SOURCE-Platform/deepreal/blender/refinements/r26/README.md

# R26 contoured roof edge

The rear roof reaches forward as a tapered leading edge while leaving the drum crowns exposed. Its underside follows the upper rear drum arc with a nominal 0.5 mm radial gap. The outer supports now reveal a curved opening at the drum ends; the center island remains between the two drums. The enclosure top and drum crowns are level at 32 mm.

## Files

- `deepreal-contoured-roof-edge-r26.blend` — editable exterior model.
- `deepreal-website-presentation-r26.blend` — model with website camera and lights.
- `r26-website-hero-dark.png` and `r26-website-hero-transparent.png` — website renders.
- `r26-roof-detail.png` — close side view of the contoured transition.
- `r26-side-preview.png` and `r26-above-preview.png` — shape review views.
- `r26-enclosure-check.json` — topology, gap profile, and sampled pose check.

This is an appearance model. The gap is visual clearance, not a validated dust seal; parting seams and fabrication tolerance remain for later work.
