SOURCE-Platform/deepreal/blender/refinements/r20/r20-interaction-desk-coverage.png

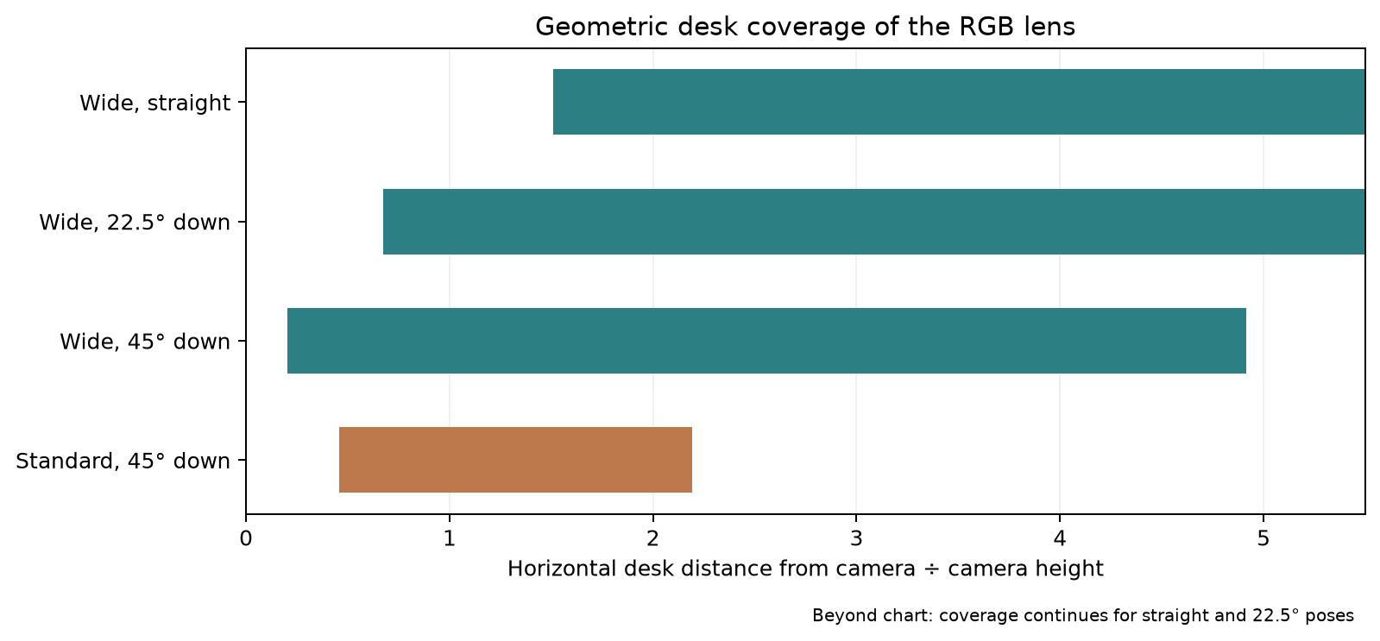
blender/refinements/r20/r20-interaction-desk-coverage.png
