SOURCE-Platform/deepreal/blender/refinements/r20/r20-wide-envelope-vs-carrier.png

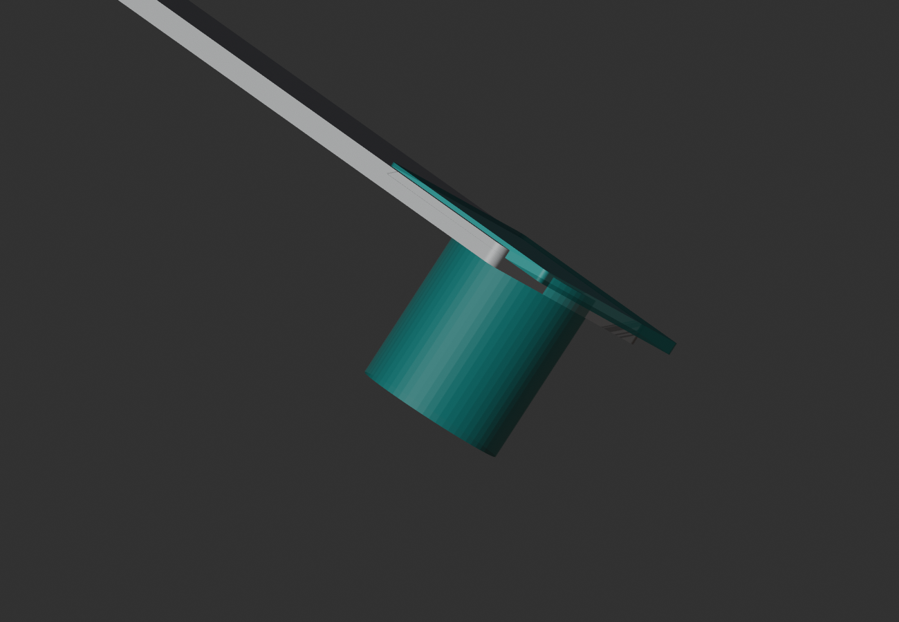
blender/refinements/r20/r20-wide-envelope-vs-carrier.png
