SOURCE-Platform/deepreal/blender/refinements/r21/r21-drive-detail-preview.png

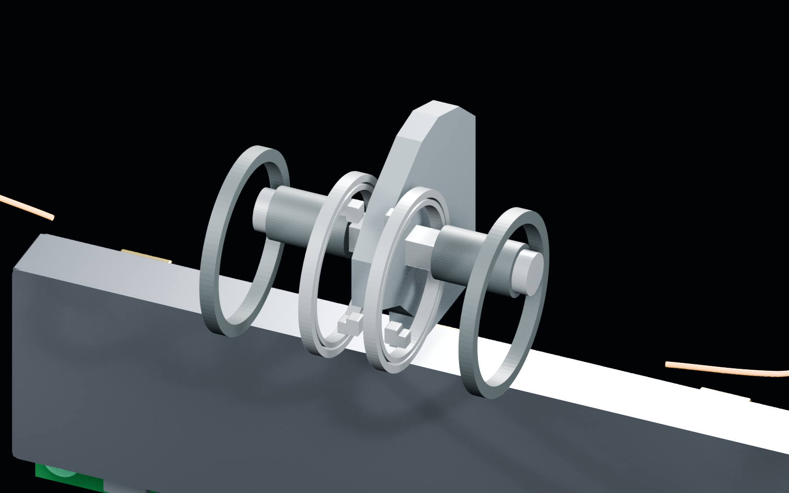
blender/refinements/r21/r21-drive-detail-preview.png
