SOURCE-Platform/deepreal/blender/refinements/r21/r21-exterior-preview.png

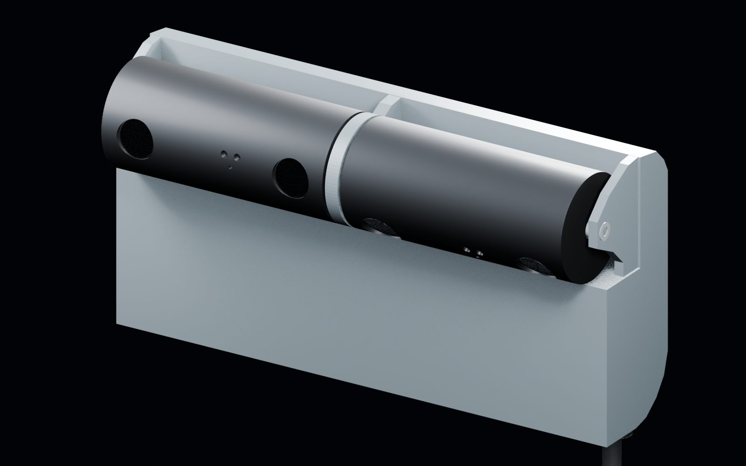
blender/refinements/r21/r21-exterior-preview.png
