SOURCE-Platform/deepreal/blender/refinements/r21/r21-front-preview.png

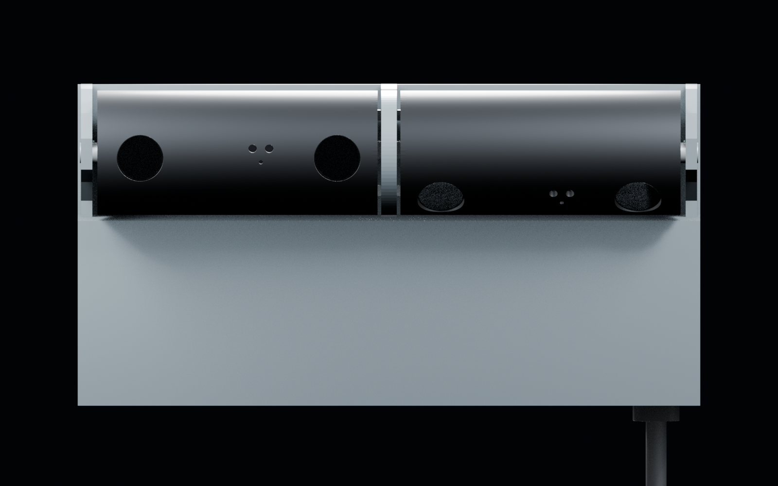
blender/refinements/r21/r21-front-preview.png
