SOURCE-Platform/deepreal/blender/refinements/r21/r21-low-pose-preview.png

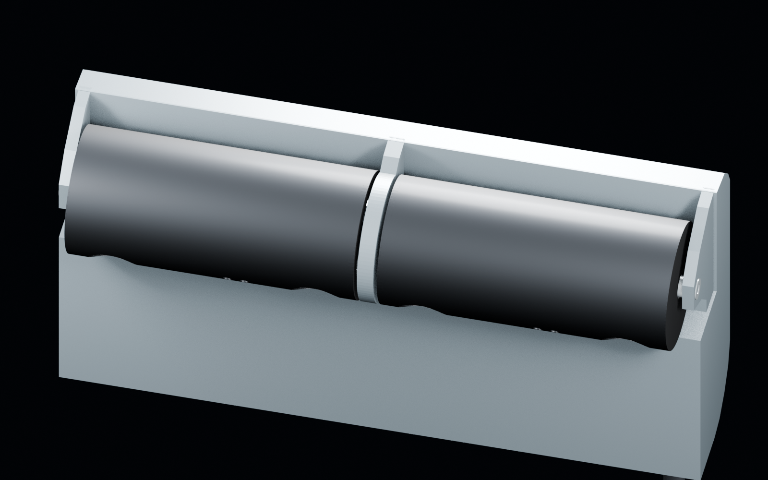
blender/refinements/r21/r21-low-pose-preview.png
