SOURCE-Platform/deepreal/blender/refinements/r22/r22-side-preview.png

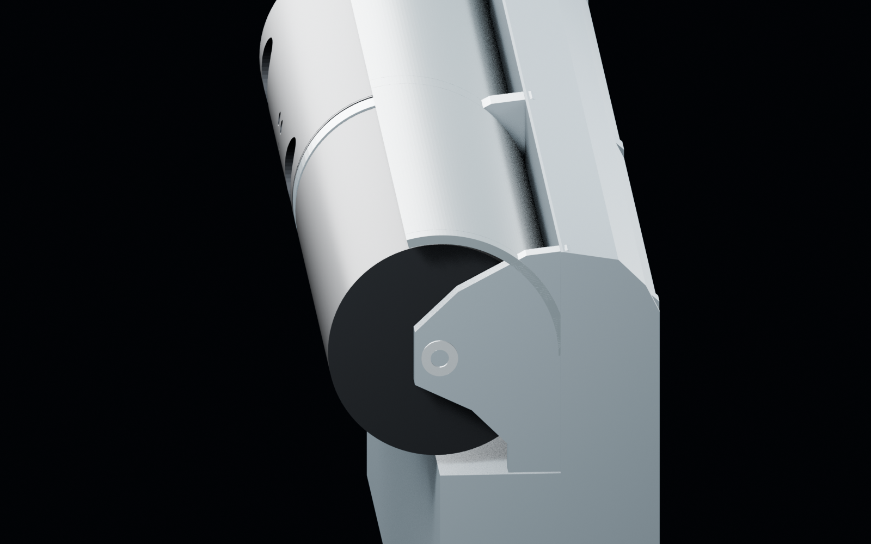
blender/refinements/r22/r22-side-preview.png
