SOURCE-Platform/deepreal/blender/refinements/r23/r23-side-preview.png

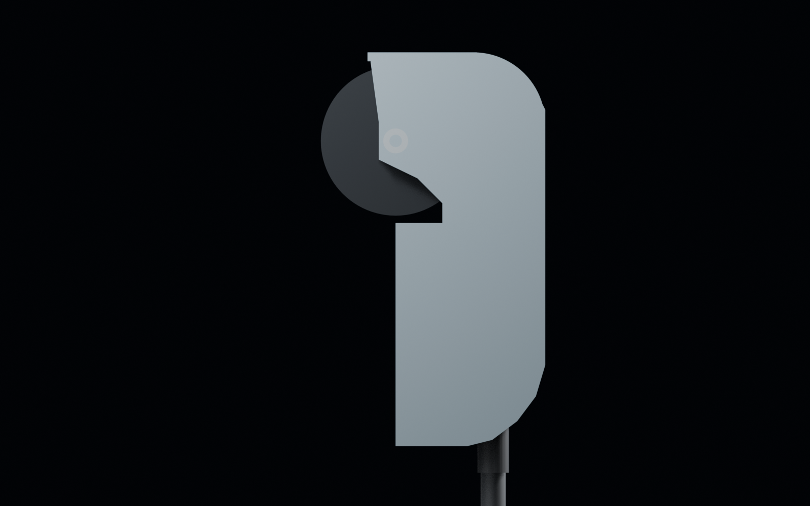
blender/refinements/r23/r23-side-preview.png
