SOURCE-Platform/deepreal/blender/refinements/r24/r24-above-preview.png

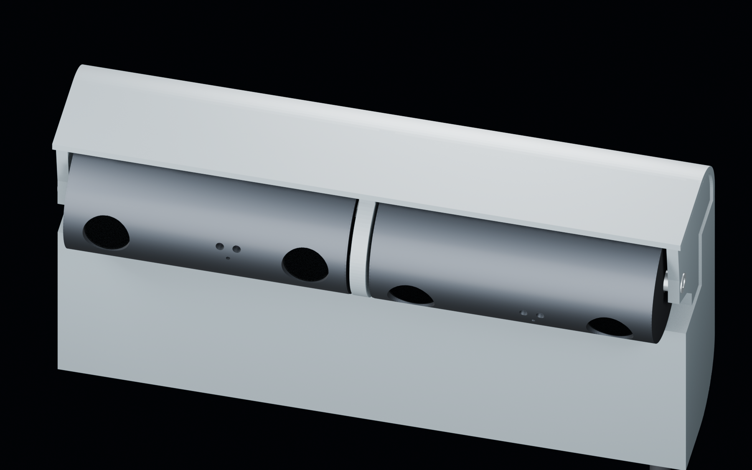
blender/refinements/r24/r24-above-preview.png
