SOURCE-Platform/deepreal/blender/refinements/r24/r24-front-preview.png

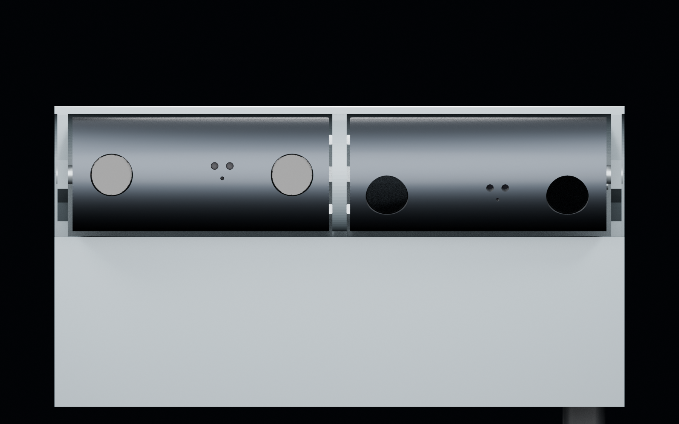
blender/refinements/r24/r24-front-preview.png
