SOURCE-Platform/deepreal/blender/refinements/r24/r24-website-hero-dark.png

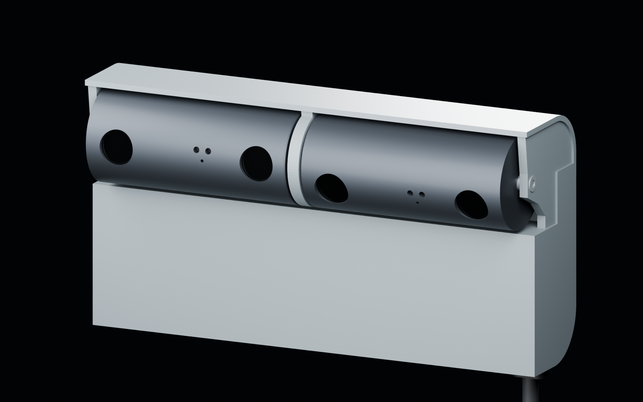
blender/refinements/r24/r24-website-hero-dark.png
