SOURCE-Platform/deepreal/blender/refinements/r24/r24-website-hero-transparent.png

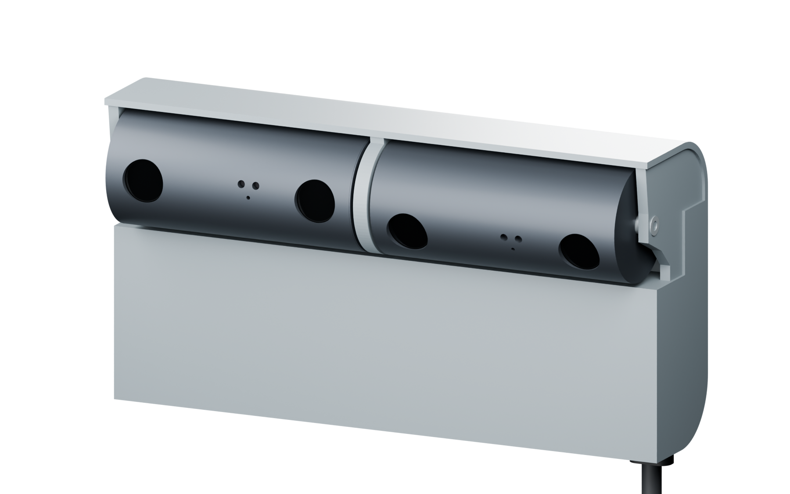
blender/refinements/r24/r24-website-hero-transparent.png
