SOURCE-Platform/deepreal/blender/refinements/r26/r26-roof-detail.png

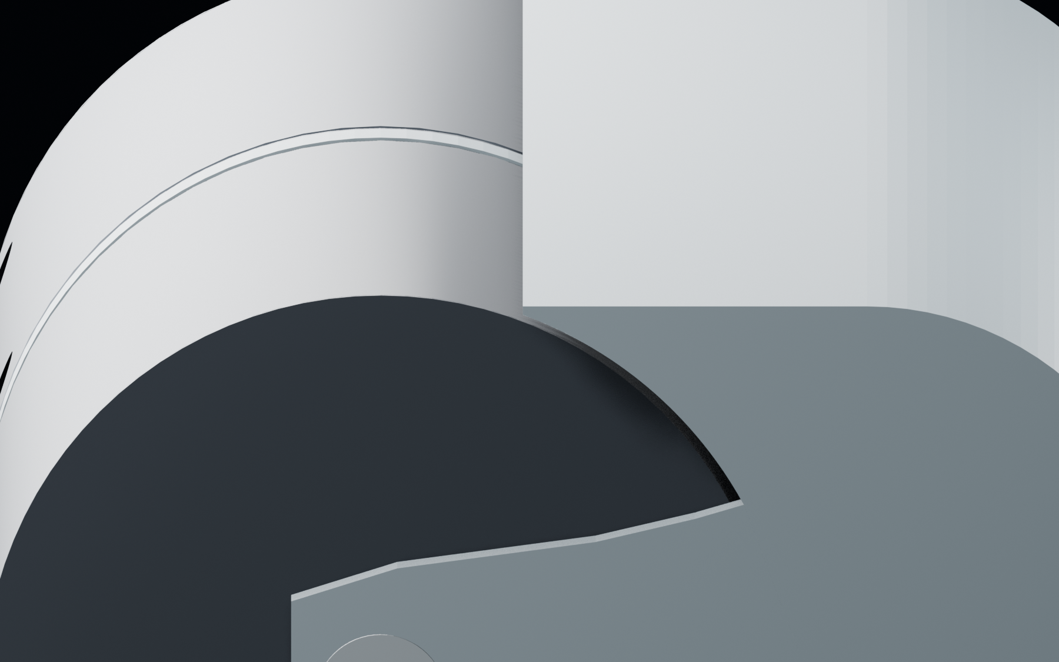
blender/refinements/r26/r26-roof-detail.png
