SOURCE-Platform/deepreal/blender/refinements/r26/r26-shell-only-front.png

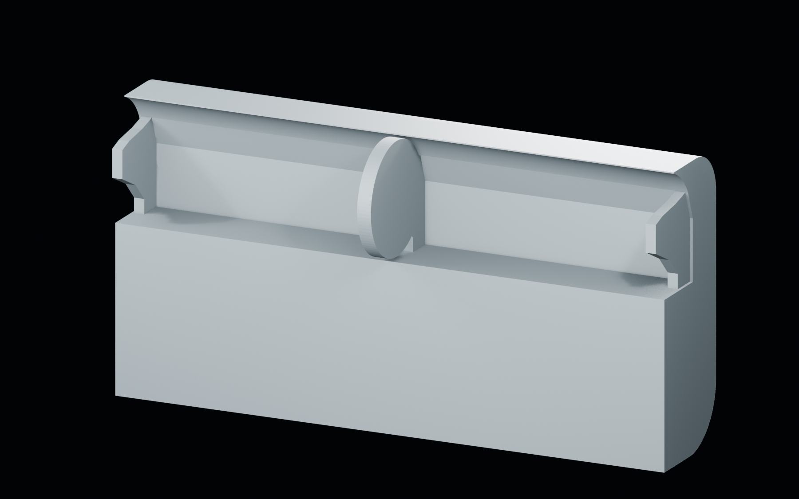
blender/refinements/r26/r26-shell-only-front.png
