SOURCE-Platform/deepreal/blender/refinements/r26/r26-shell-only-low.png

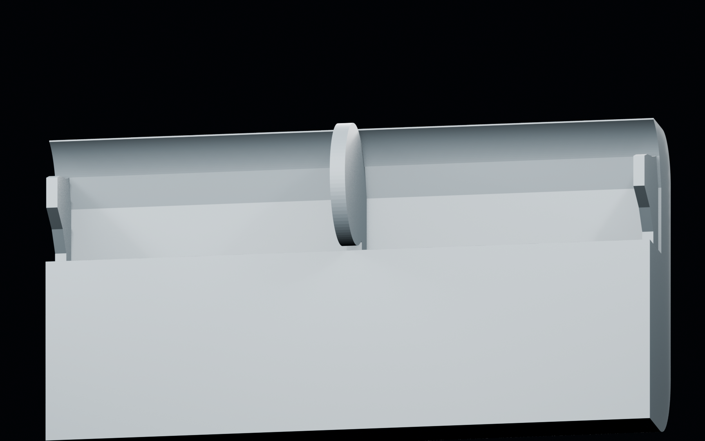
blender/refinements/r26/r26-shell-only-low.png
