SOURCE-Platform/deepreal/blender/refinements/r28/r28-connected-shell-low.png

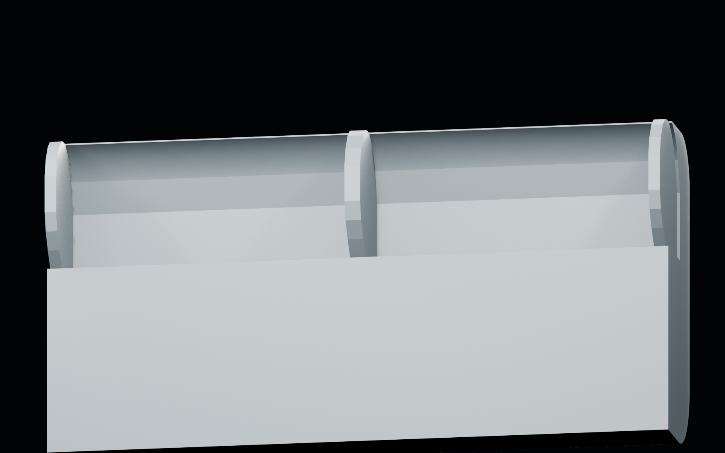
blender/refinements/r28/r28-connected-shell-low.png
