SOURCE-Platform/deepreal/blender/refinements/r28/r28-connected-shell.png

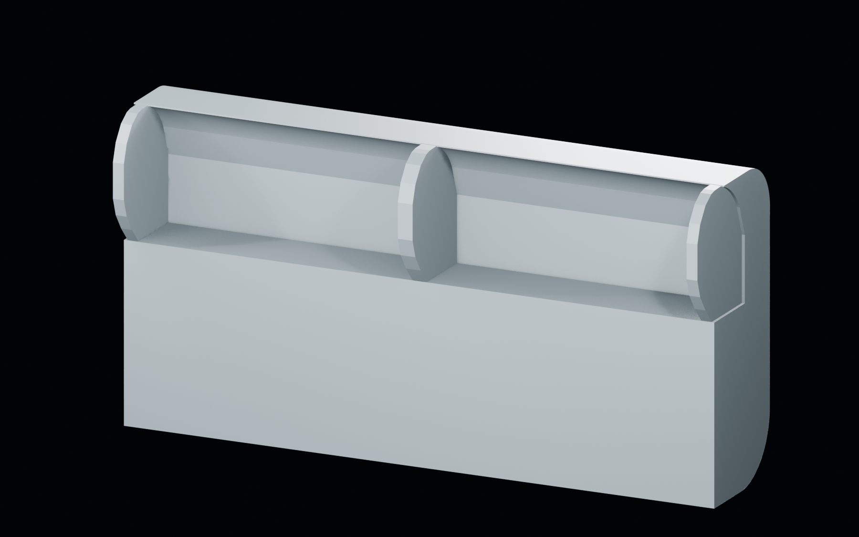
blender/refinements/r28/r28-connected-shell.png
