SOURCE-Platform/deepreal/blender/refinements/r28/r28-three-dividers-shell.png

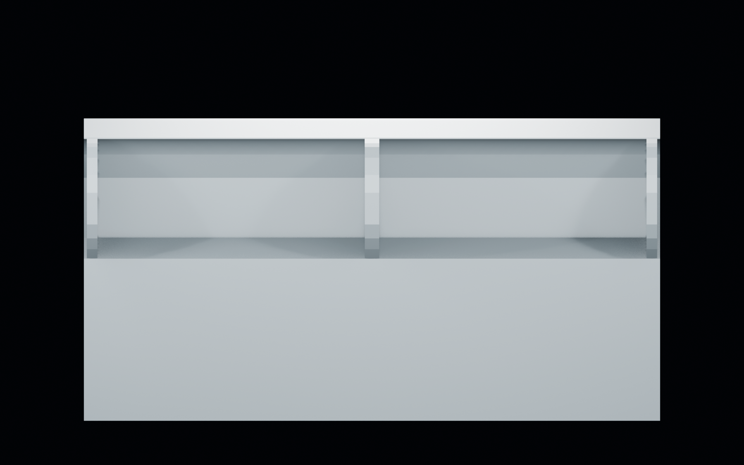
blender/refinements/r28/r28-three-dividers-shell.png
