SOURCE-Platform/deepreal/blender/refinements/r29/r29-center-divider-detail.png

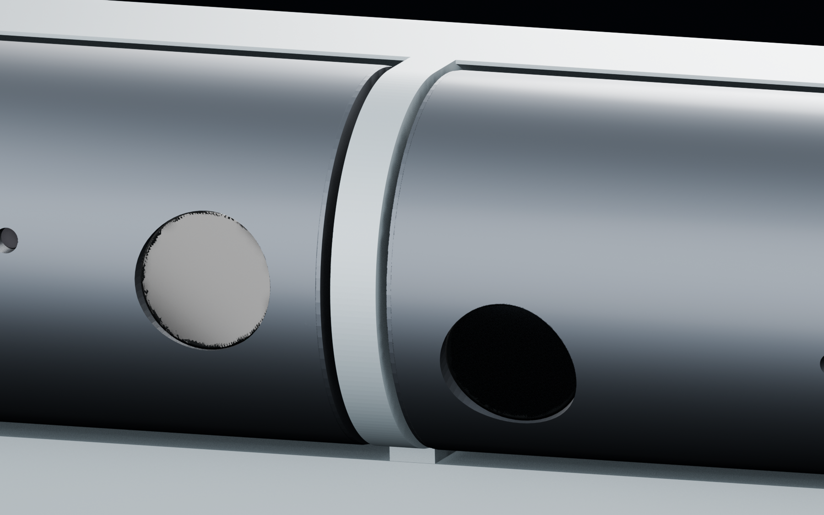
blender/refinements/r29/r29-center-divider-detail.png
