SOURCE-Platform/deepreal/blender/refinements/r29/r29-connected-shell-low.png

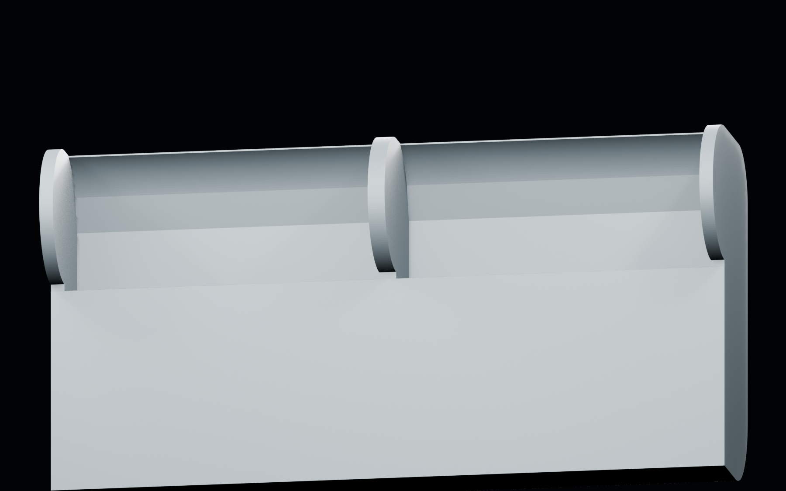
blender/refinements/r29/r29-connected-shell-low.png
