SOURCE-Platform/deepreal/blender/refinements/r29/r29-right-side-detail.png

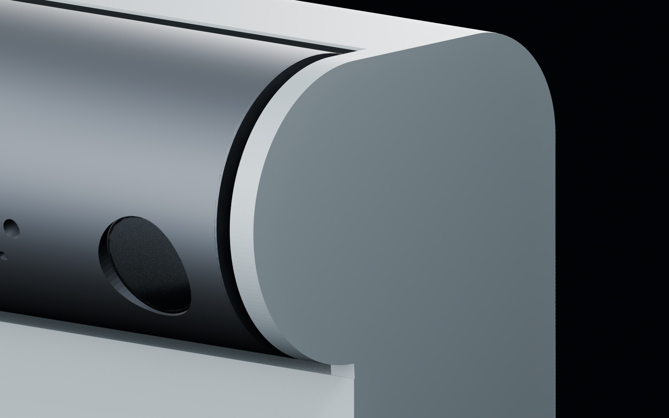
blender/refinements/r29/r29-right-side-detail.png
