SOURCE-Platform/deepreal/blender/refinements/r29/r29-three-dividers-shell.png

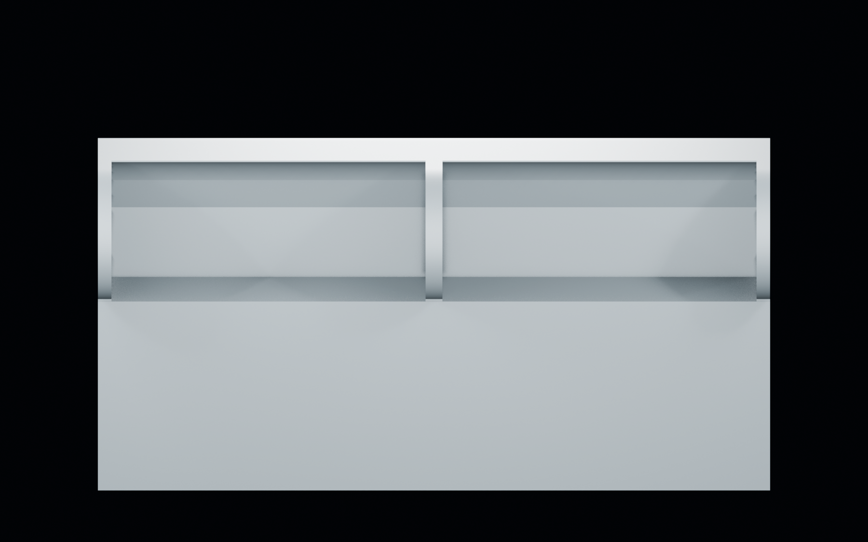
blender/refinements/r29/r29-three-dividers-shell.png
