SOURCE-Platform/deepreal/blender/refinements/r30/r30-ledge-detail.png

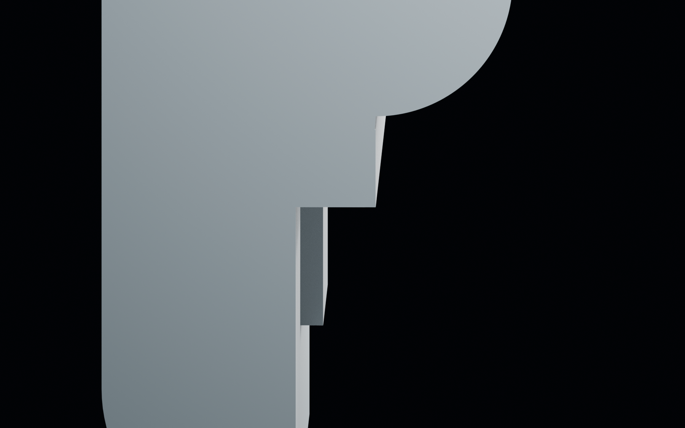
blender/refinements/r30/r30-ledge-detail.png
