SOURCE-Platform/deepreal/blender/refinements/r30/r30-monitor-mount-section.png

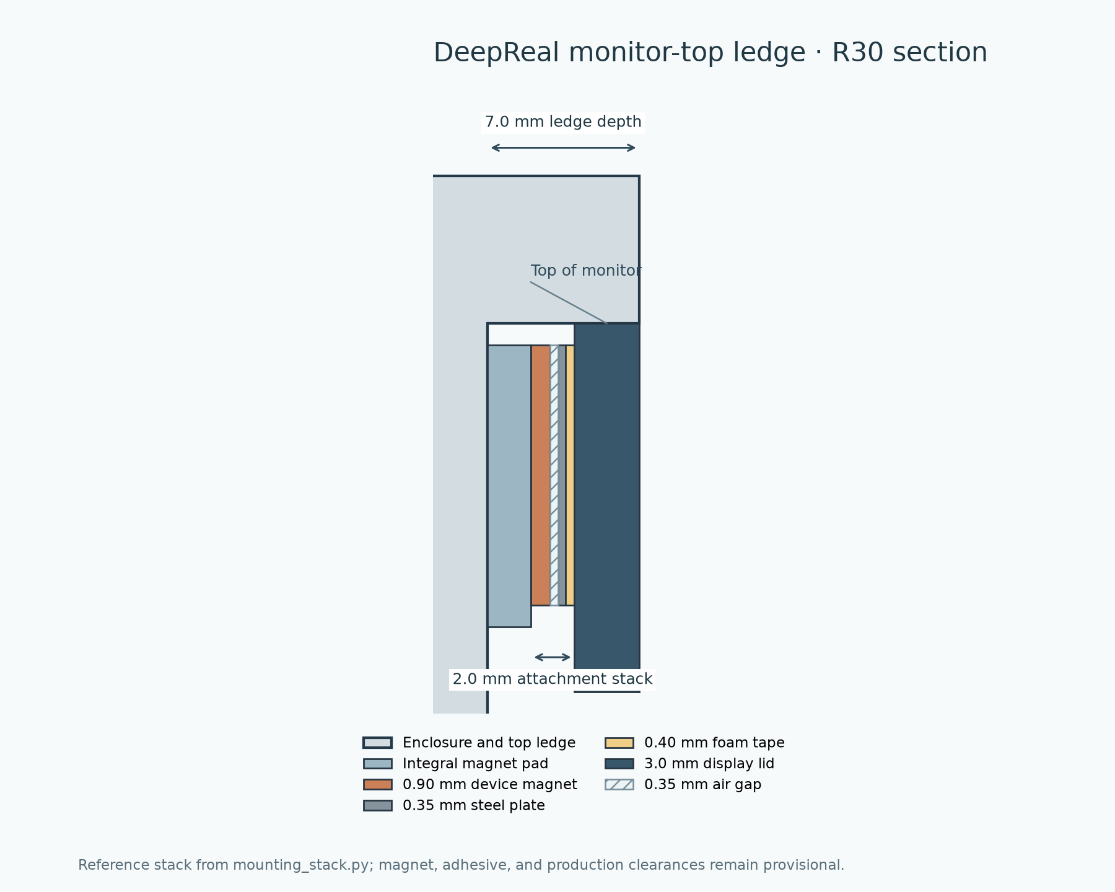
blender/refinements/r30/r30-monitor-mount-section.png
