SOURCE-Platform/deepreal/blender/refinements/r30/r30-side-profile.png

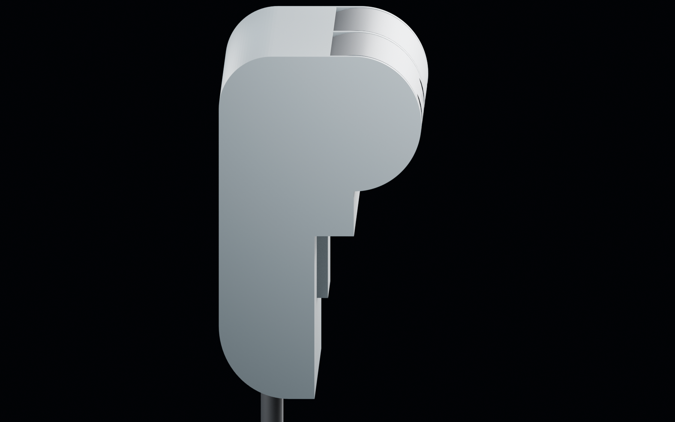
blender/refinements/r30/r30-side-profile.png
