SOURCE-Platform/deepreal/blender/refinements/r31/r31-attachment-layers-exploded.png

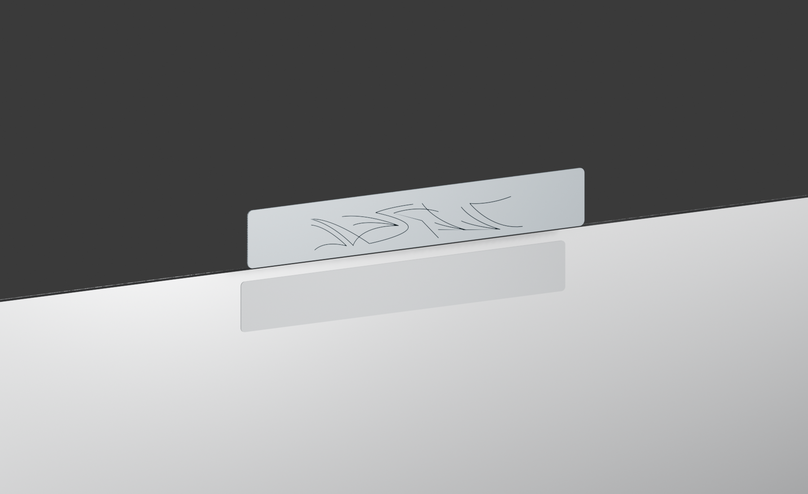
blender/refinements/r31/r31-attachment-layers-exploded.png
