SOURCE-Platform/deepreal/blender/refinements/r31/r31-full-width-plate.png

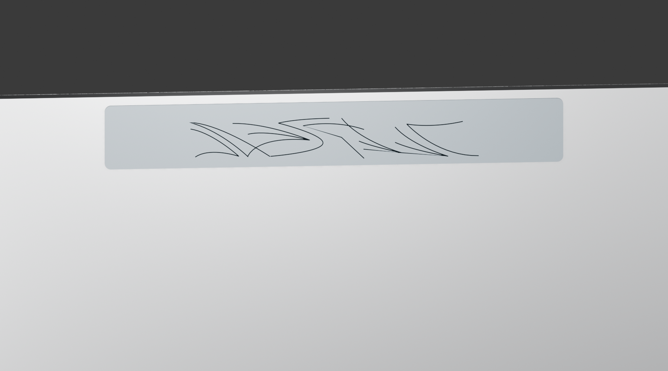
blender/refinements/r31/r31-full-width-plate.png
