SOURCE-Platform/deepreal/blender/refinements/r31/r31-laptop-back.png

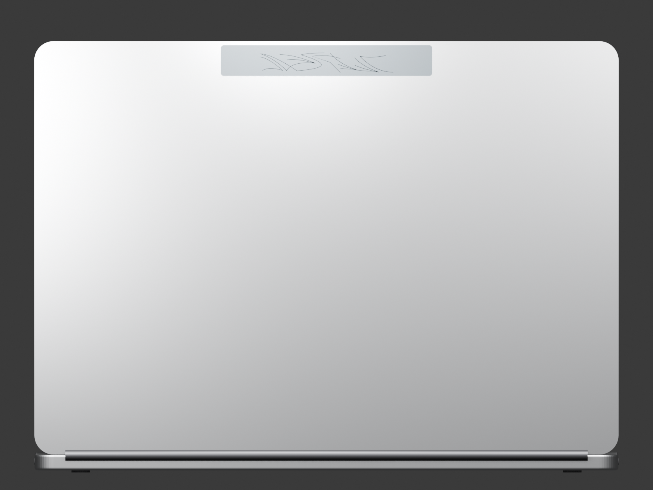
blender/refinements/r31/r31-laptop-back.png
