SOURCE-Platform/deepreal/blender/refinements/r32/r32-groove-shadow-detail.png

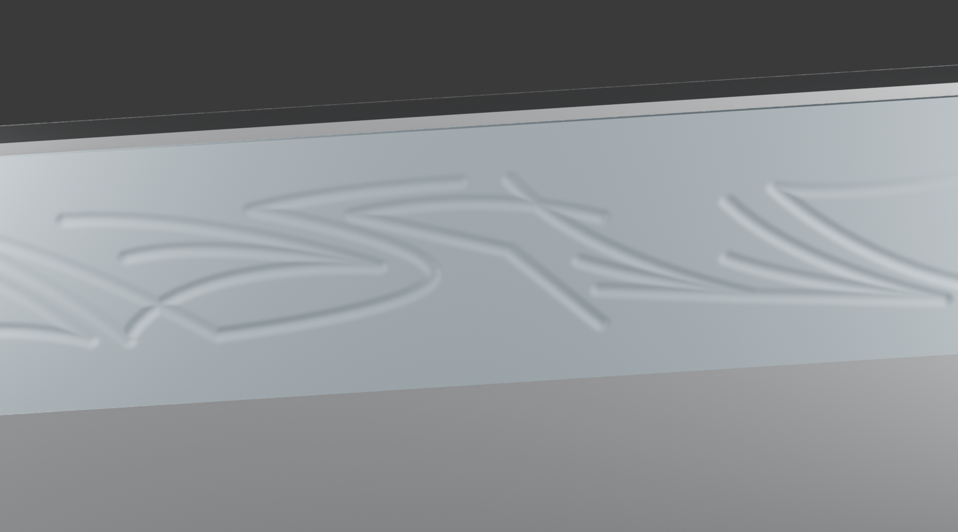
blender/refinements/r32/r32-groove-shadow-detail.png
