SOURCE-Platform/deepreal/blender/refinements/r32/r32-laptop-back.png

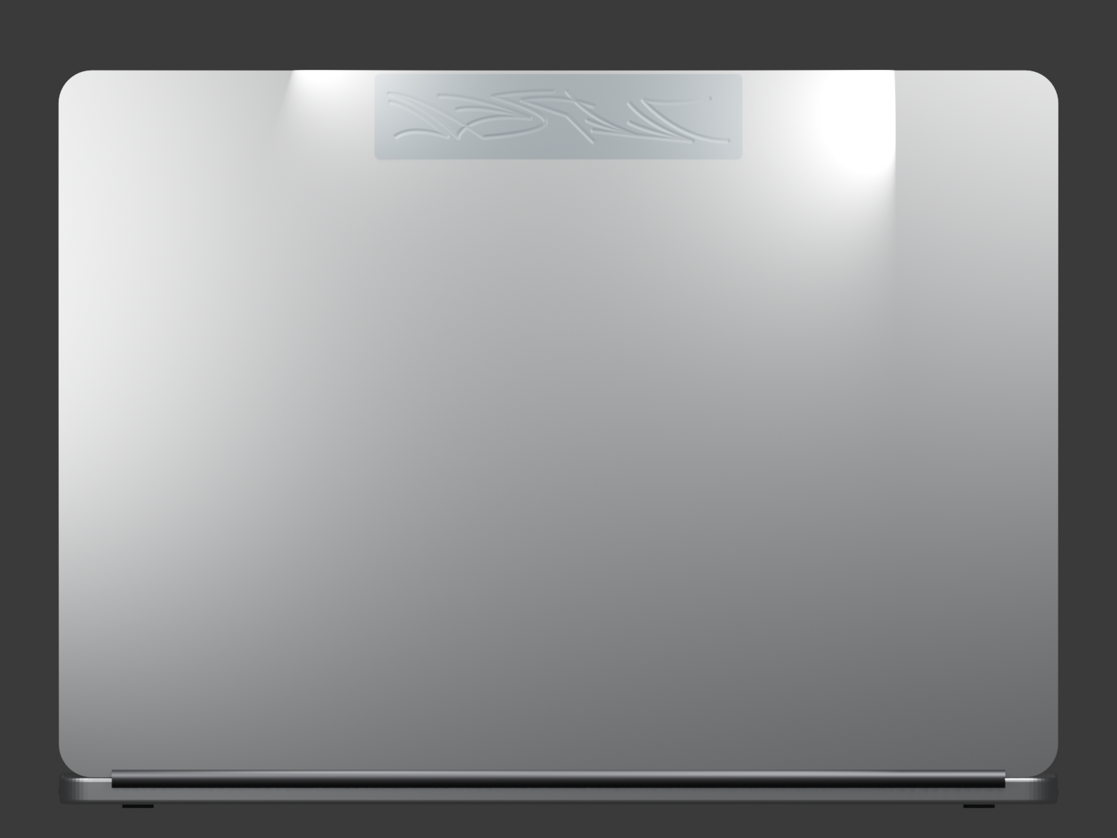
blender/refinements/r32/r32-laptop-back.png
