SOURCE-Platform/deepreal/blender/refinements/r32/r32-tall-pressed-plate.png

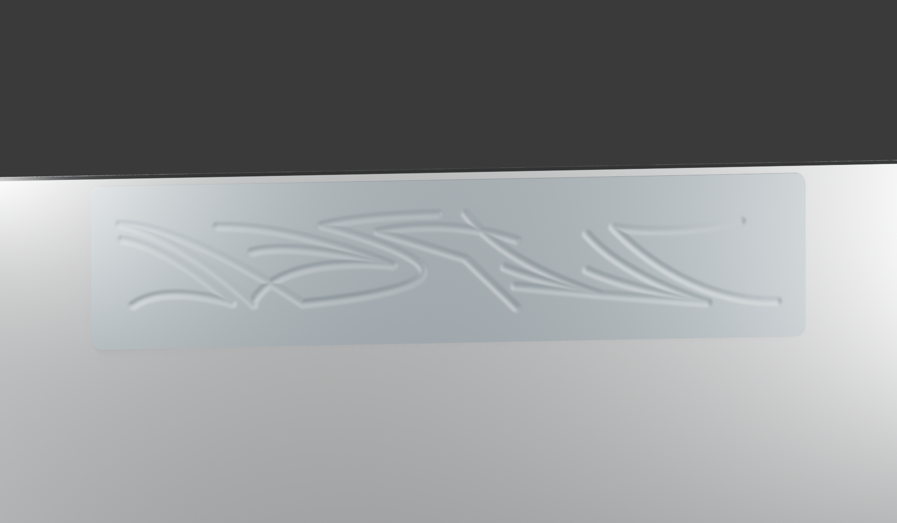
blender/refinements/r32/r32-tall-pressed-plate.png
