SOURCE-Platform/deepreal/blender/refinements/r33/r33-moving-sheen-preview.gif

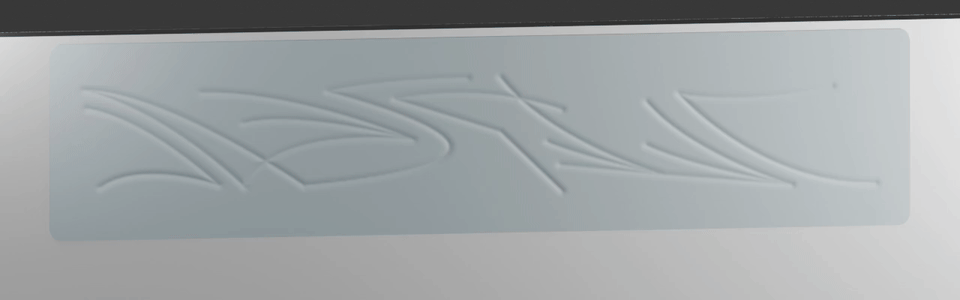
blender/refinements/r33/r33-moving-sheen-preview.gif
