SOURCE-Platform/deepreal/blender/refinements/r33/r33-profile-comparison.png

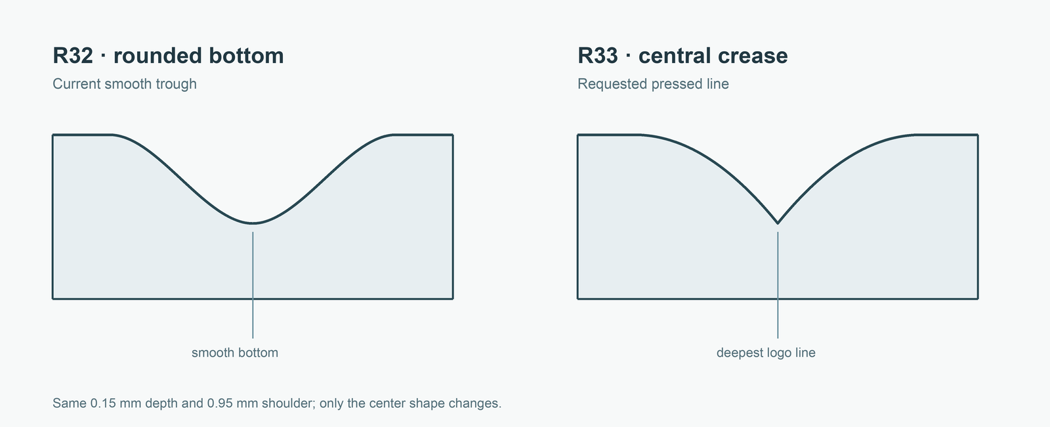
blender/refinements/r33/r33-profile-comparison.png
