SOURCE-Platform/deepreal/blender/refinements/r34/r34-inner-flex-detail.png

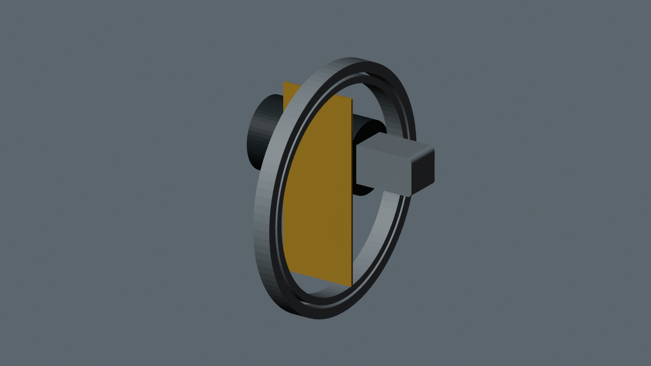
blender/refinements/r34/r34-inner-flex-detail.png
