SOURCE-Platform/deepreal/blender/refinements/r34/r34-mechanism-study.png

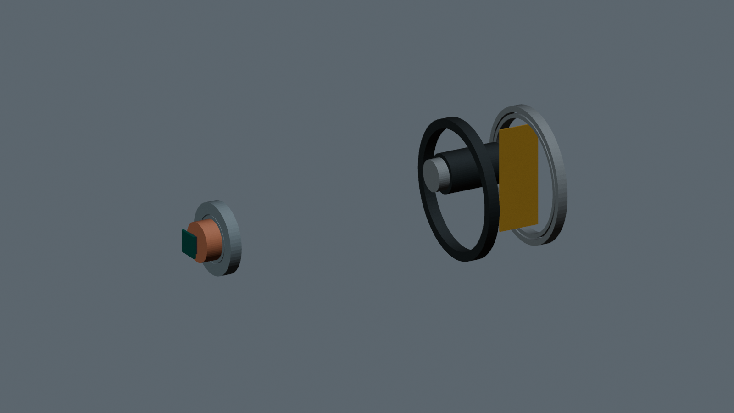
blender/refinements/r34/r34-mechanism-study.png
