SOURCE-Platform/deepreal/blender/refinements/r34/r34-outer-encoder-detail.png

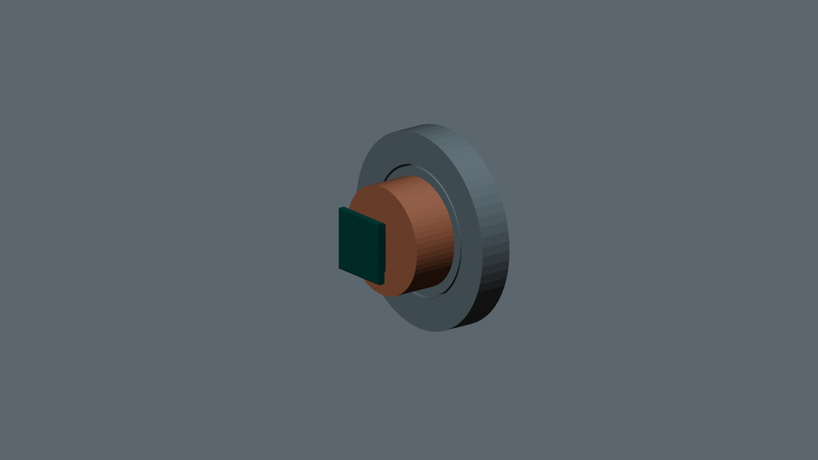
blender/refinements/r34/r34-outer-encoder-detail.png
