SOURCE-Platform/deepreal/blender/refinements/r35/r35-flex-center-conflict.png

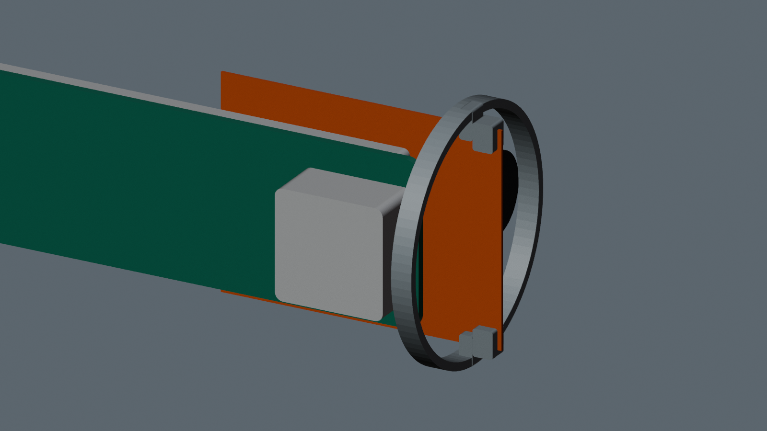
blender/refinements/r35/r35-flex-center-conflict.png
