SOURCE-Platform/deepreal/blender/refinements/r35/r35-flex-up45-conflict.png

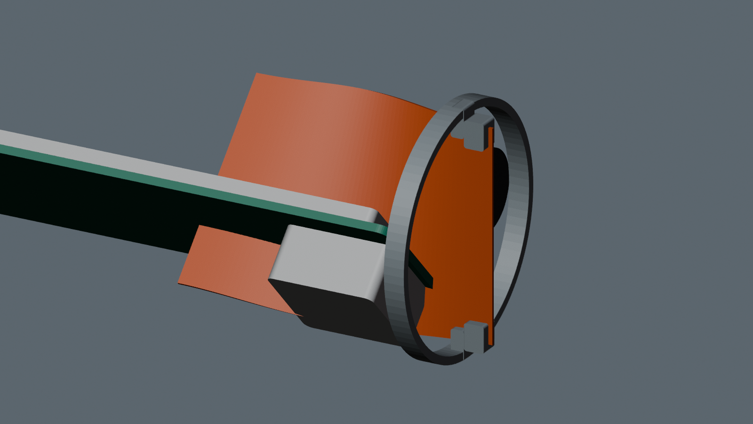
blender/refinements/r35/r35-flex-up45-conflict.png
