SOURCE-Platform/deepreal/blender/refinements/r35/r35-outer-load-path.png

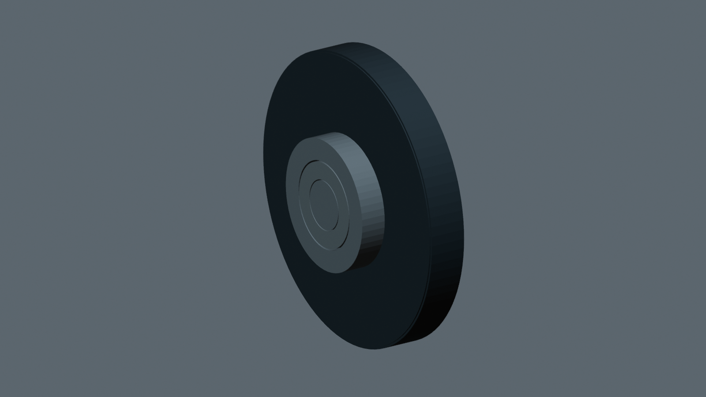
blender/refinements/r35/r35-outer-load-path.png
