SOURCE-Platform/deepreal/blender/refinements/r36/r36-bearing-window-end.png

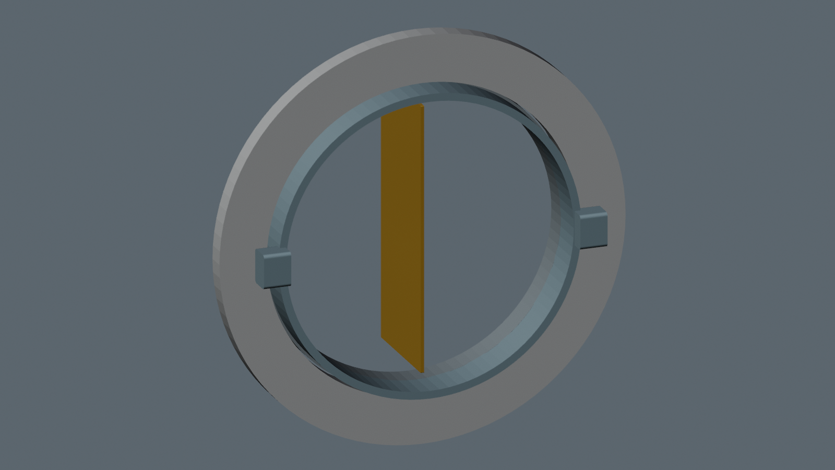
blender/refinements/r36/r36-bearing-window-end.png
