SOURCE-Platform/deepreal/blender/refinements/r36/r36-bearing-window-side.png

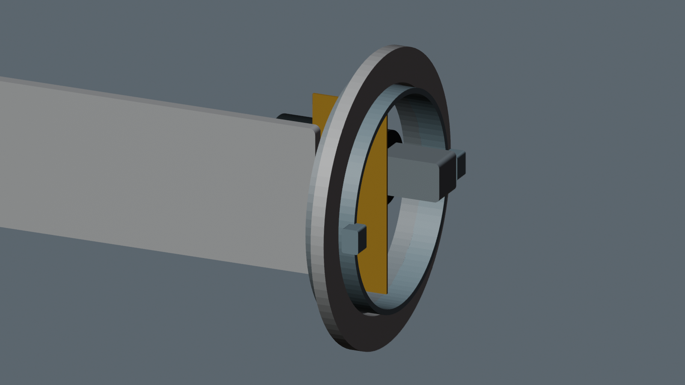
blender/refinements/r36/r36-bearing-window-side.png
