SOURCE-Platform/deepreal/blender/refinements/r37/r37-rear-volume-internal.png

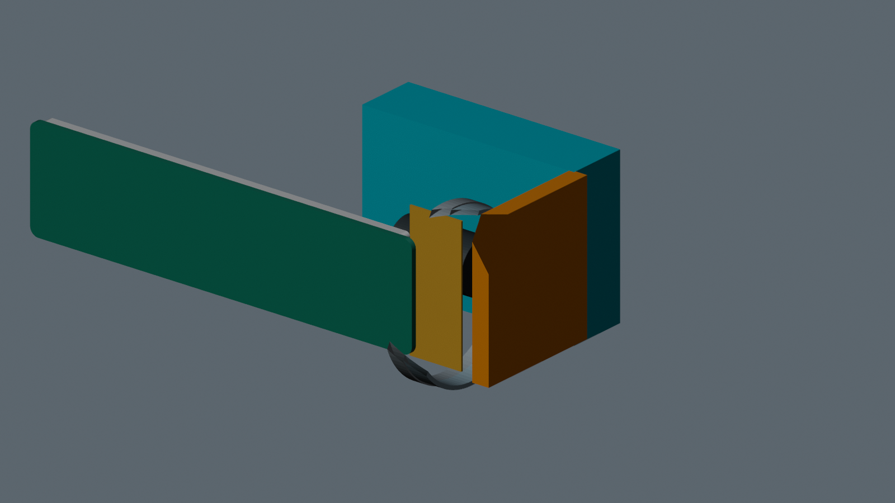
blender/refinements/r37/r37-rear-volume-internal.png
