SOURCE-Platform/deepreal/blender/refinements/r38/r38-usb-plug-detail.png

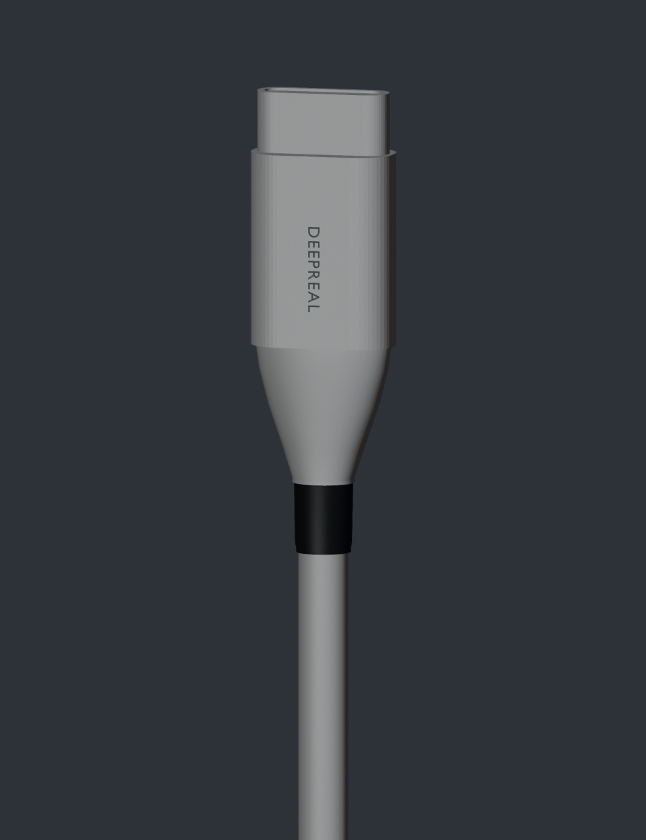
blender/refinements/r38/r38-usb-plug-detail.png
