SOURCE-Platform/deepreal/docs/design/blender-electronics-shield.png

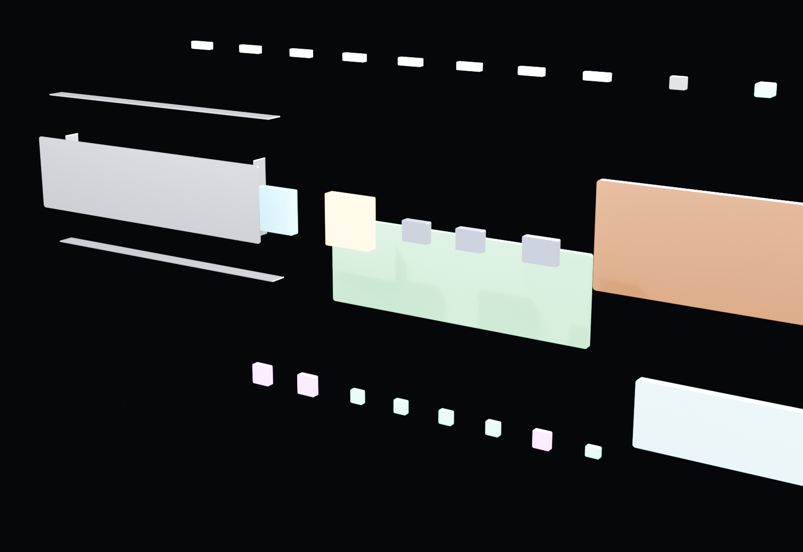
docs/design/blender-electronics-shield.png
