SOURCE-Platform/deepreal/docs/design/blender-four-view-overview.png

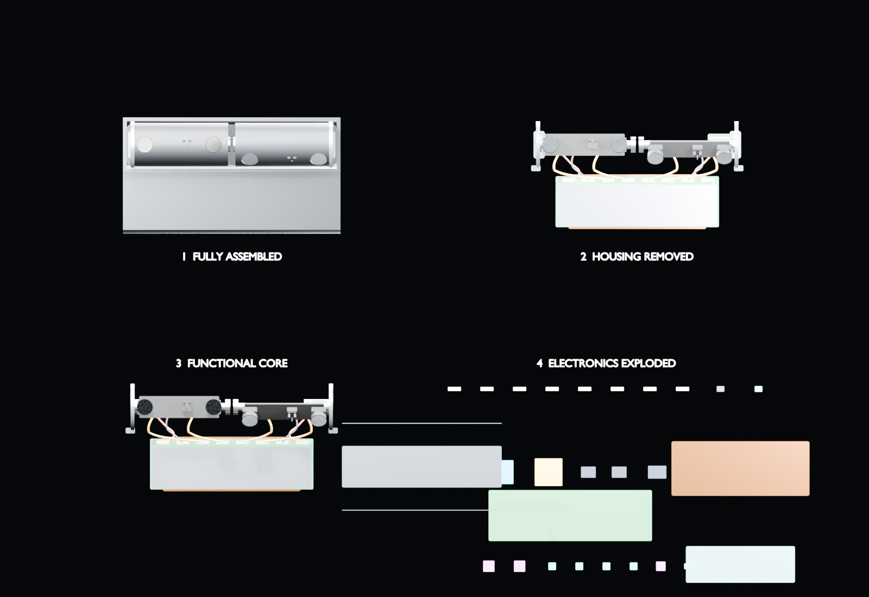
docs/design/blender-four-view-overview.png
