SOURCE-Platform/deepreal/references/components/datasheets/robotis-xl330-m288-drawing.png

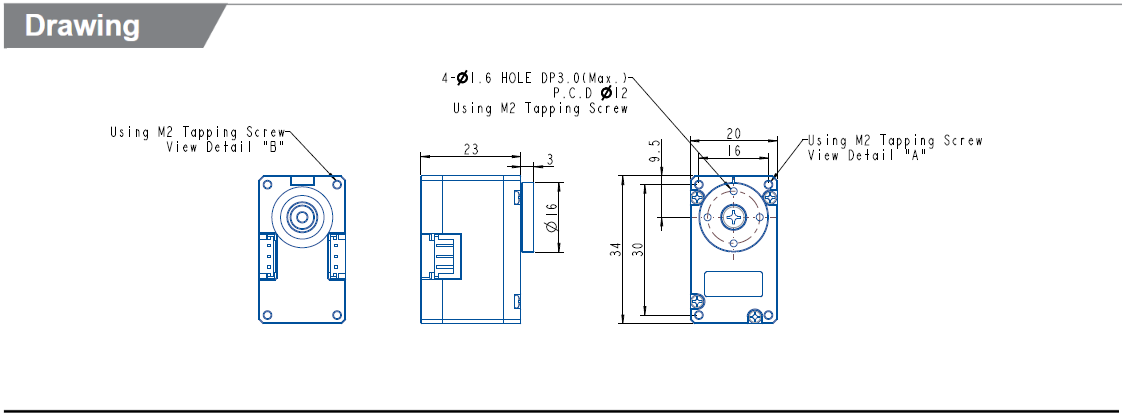
references/components/datasheets/robotis-xl330-m288-drawing.png
