SOURCE-Platform/deepreal/references/components/datasheets/tmotor-gb2208-drawing.jpg

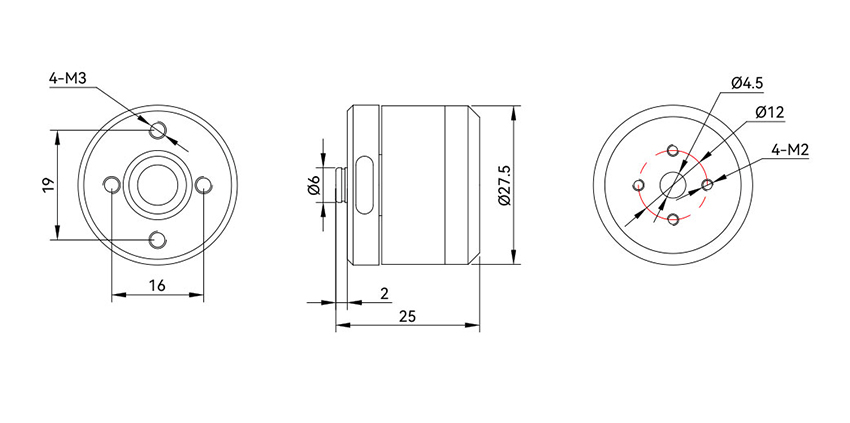
references/components/datasheets/tmotor-gb2208-drawing.jpg
