SOURCE-Platform/deepreal/blender/refinements/r28/r28-three-dividers-assembled.png

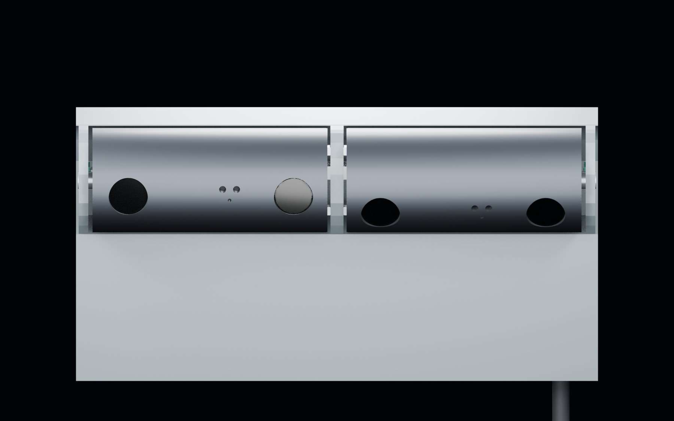
blender/refinements/r28/r28-three-dividers-assembled.png
