SOURCE-Platform/deepreal/blender/refinements/r30/r30-assembled-preview.png

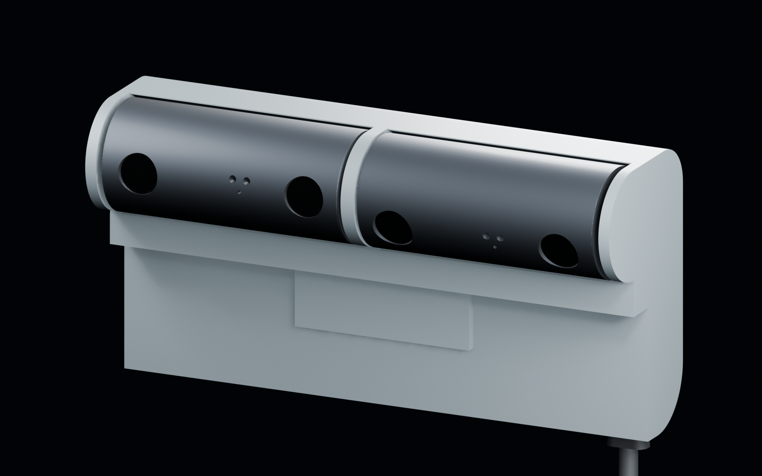
blender/refinements/r30/r30-assembled-preview.png
