SOURCE-Platform/deepreal/docs/design/blender-fully-assembled.png

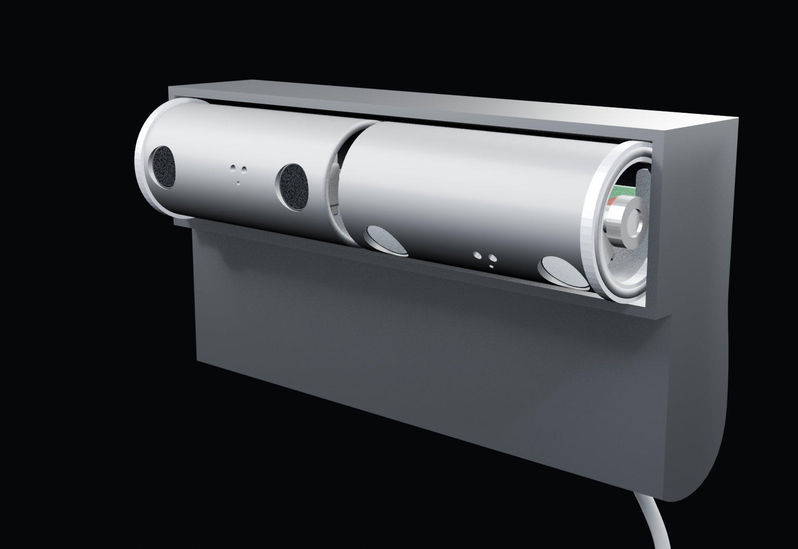
docs/design/blender-fully-assembled.png
